efabless/raven-picorv32/verilog/raven_cam/cam.c

#include "cam.h"
#include "spi_io.h"
#include "i2c_io.h"

extern void print(const char *p);
extern void print_hex(uint32_t v, int digits);

void _delay_ms(int v) {
    for (int j = 0; j < 170 * v; j++);
}

bool check_spi() {
    uint8_t data;
    // test spi with write and read from test register
    write_spi_slave(0x00, 0x55);
    data = read_spi_slave_byte(0x00);
    if (data == 0x55) {
        return true;
    }
    return false;
}

bool check_camera(uint32_t *vid, uint32_t *pid) {
//    uint8_t vid, pid;
    write_sensor_reg(0xff, 0x01);
    read_sensor_reg(OV2640_CHIPID_HIGH, vid);
    read_sensor_reg(OV2640_CHIPID_LOW, pid);
    *vid &= (uint8_t) 0xff;
    *pid &= (uint8_t) 0xff;
    if ((*vid == 0x26 ) && ((*pid == 0x41 ) || (*pid == 0x42 )))
        return true;
    else
        return false;
}

void reset_cpld() {
    write_reg(0x07, 0x80);
    _delay_ms(1000);
    write_reg(0x07, 0x00);
    _delay_ms(1000);
}

void init_camera() {
    write_sensor_reg(0xff, 0x01);
    write_sensor_reg(0x12, 0x80);
    _delay_ms(1000);

    print("jpeg init\n");
    write_sensor_reg_list(OV2640_JPEG_INIT, true);

    print("yuv422\n");
    write_sensor_reg_list(OV2640_YUV422, true);

    print("ov2640 jpeg\n");
    write_sensor_reg_list(OV2640_JPEG, true);

    write_sensor_reg(0xff, 0x01);
    write_sensor_reg(0x15, 0x00);
    write_sensor_reg_list(OV2640_160x120_JPEG, true);
//    write_sensor_reg_list(OV2640_320x240_JPEG, true);
    write_sensor_reg(0xff, 0x00);
    write_sensor_reg(0x44, 0x32);

//    write_sensor_reg_list(OV2640_QVGA);
    _delay_ms(1000);

}

void set_frame_count() {
    write_reg(0x01, 0x00); // set frame count to 1
    write_reg(0x02, 0x00); // set LCD bus mode to MCU
    _delay_ms(1000);
}

void flush_fifo(void) {
	write_reg(ARDUCHIP_FIFO, FIFO_CLEAR_MASK);
//	write_reg(ARDUCHIP_FIFO, FIFO_RDPTR_RST_MASK);
//	write_reg(ARDUCHIP_FIFO, FIFO_RDPTR_RST_MASK | FIFO_WRPTR_RST_MASK);
}

void reset_fifo_read_ptr(void) {
	write_reg(ARDUCHIP_FIFO, FIFO_RDPTR_RST_MASK);
//	write_reg(ARDUCHIP_FIFO, FIFO_RDPTR_RST_MASK | FIFO_WRPTR_RST_MASK);
}

void start_capture(void) {
	write_reg(ARDUCHIP_FIFO, FIFO_START_MASK);
}

void clear_fifo_flag(void) {
	write_reg(ARDUCHIP_FIFO, FIFO_CLEAR_MASK);
}

uint8_t read_fifo(void) {}

uint8_t read_reg(uint32_t addr) {
    return read_spi_slave_byte(addr);
}

void write_reg(uint32_t addr, uint32_t data) {
    write_spi_slave(addr, data);
}

void write_sensor_reg(uint32_t addr, uint32_t data) {
    write_i2c_slave(SENSOR_ADDR, addr, data);
}

void read_sensor_reg(uint32_t addr, uint32_t* data) {
    *data = read_i2c_slave_byte(SENSOR_ADDR, addr) & (uint32_t) 0x00ff;
}

bool write_sensor_reg_list(const struct sensor_reg reglist[], bool verify) {
    uint32_t reg_addr = 0;
    uint32_t reg_val = 0, data;
    const struct sensor_reg *next = reglist;
    bool status = true;
    while ((reg_addr != 0xff) || (reg_val != 0xff))
    {
        reg_addr = next->reg;
        reg_val = next->val;
        write_sensor_reg(reg_addr, reg_val);
        if (verify) {
            read_sensor_reg(reg_addr, &data);
            if (data != reg_val) {
                print("error@0x"); print_hex(reg_addr, 2);
                print("=0x"); print_hex(data, 2);
                print(" ( 0x"); print_hex(reg_val, 2);
                print(" )\n");
                status = false;
            }
        }
        next++;
    }
    _delay_ms(1000);
    return status;
}

uint32_t read_fifo_length()
{
	uint32_t len1,len2,len3,length=0;
	len1 = read_reg(FIFO_SIZE1);
    len2 = read_reg(FIFO_SIZE2);
    len3 = read_reg(FIFO_SIZE3) & 0x7f;
    length = ((len3 << 16) | (len2 << 8) | len1) & 0x07fffff;
	return length;
}

bool set_JPEG_size(uint8_t size) {
    switch(size) {
        case OV2640_160x120:
            return write_sensor_reg_list(OV2640_160x120_JPEG, true);
        case OV2640_640x480:
            return write_sensor_reg_list(OV2640_640x480_JPEG, true);
        case OV2640_800x600:
            return write_sensor_reg_list(OV2640_800x600_JPEG, true);
        case OV2640_320x240:
        default:
            return write_sensor_reg_list(OV2640_320x240_JPEG, true);
    }

}

void set_Light_Mode(uint8_t Light_Mode) {}
void set_Color_Saturation(uint8_t Color_Saturation) {}
void set_Brightness(uint8_t Brightness) {}
void set_Contrast(uint8_t Contrast) {}
void set_Special_effects(uint8_t Special_effect) {}

const char bmp_header[BMPIMAGEOFFSET] PROGMEM =
{
  0x42, 0x4D, 0x36, 0x58, 0x02, 0x00, 0x00, 0x00, 0x00, 0x00, 0x42, 0x00, 0x00, 0x00, 0x28, 0x00,
  0x00, 0x00, 0x40, 0x01, 0x00, 0x00, 0xF0, 0x00, 0x00, 0x00, 0x01, 0x00, 0x10, 0x00, 0x03, 0x00,
  0x00, 0x00, 0x00, 0x58, 0x02, 0x00, 0xC4, 0x0E, 0x00, 0x00, 0xC4, 0x0E, 0x00, 0x00, 0x00, 0x00,
  0x00, 0x00, 0x00, 0x00, 0x00, 0x00, 0x00, 0xF8, 0x00, 0x00, 0xE0, 0x07, 0x00, 0x00, 0x1F, 0x00,
  0x00, 0x00
};

const struct sensor_reg OV2640_JPEG_INIT[] PROGMEM =
{
  { 0xff, 0x00 },
  { 0x2c, 0xff },
  { 0x2e, 0xdf },
  { 0xff, 0x01 },
  { 0x3c, 0x32 },
  { 0x11, 0x00 },
  { 0x09, 0x02 },
  { 0x04, 0x28 },
  { 0x13, 0xe5 },
  { 0x14, 0x48 },
  { 0x2c, 0x0c },
  { 0x33, 0x78 },
  { 0x3a, 0x33 },
  { 0x3b, 0xfB },
  { 0x3e, 0x00 },
  { 0x43, 0x11 },
  { 0x16, 0x10 },
  { 0x39, 0x92 },
  { 0x35, 0xda },
  { 0x22, 0x1a },
  { 0x37, 0xc3 },
  { 0x23, 0x00 },
  { 0x34, 0xc0 },
  { 0x36, 0x1a },
  { 0x06, 0x88 },
  { 0x07, 0xc0 },
  { 0x0d, 0x87 },
  { 0x0e, 0x41 },
  { 0x4c, 0x00 },
  { 0x48, 0x00 },
  { 0x5B, 0x00 },
  { 0x42, 0x03 },
  { 0x4a, 0x81 },
  { 0x21, 0x99 },
  { 0x24, 0x40 },
  { 0x25, 0x38 },
  { 0x26, 0x82 },
  { 0x5c, 0x00 },
  { 0x63, 0x00 },
  { 0x61, 0x70 },
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

  { 0x12, 0x40 },
  { 0xd3, 0x04 },	//{ 0xd3, 0x7f },
  { 0xc0, 0x16 },
  { 0xC1, 0x12 },
  { 0x8c, 0x00 },
  { 0x86, 0x3d },
  { 0x50, 0x00 },
  { 0x51, 0x2C },
  { 0x52, 0x24 },
  { 0x53, 0x00 },
  { 0x54, 0x00 },
  { 0x55, 0x00 },
  { 0x5A, 0x2c },
  { 0x5b, 0x24 },
  { 0x5c, 0x00 },
  { 0xff, 0xff },
};

const struct sensor_reg OV2640_JPEG[] PROGMEM =
{
  { 0xe0, 0x14 },
  { 0xe1, 0x77 },
  { 0xe5, 0x1f },
  { 0xd7, 0x03 },
  { 0xda, 0x10 },
  { 0xe0, 0x00 },
  { 0xFF, 0x01 },
  { 0x04, 0x08 },
  { 0xff, 0xff },
};

const struct sensor_reg OV2640_YUV422[] PROGMEM =
{
  { 0xFF, 0x00 },
  { 0x05, 0x00 },
  { 0xDA, 0x10 },
  { 0xD7, 0x03 },
  { 0xDF, 0x00 },
  { 0x33, 0x80 },
  { 0x3C, 0x40 },
  { 0xe1, 0x77 },
  { 0x00, 0x00 },
  { 0xff, 0xff },
};

/* JPG 160x120 */
const struct sensor_reg OV2640_160x120_JPEG[] PROGMEM =
{
  { 0xff, 0x01 },
  { 0x12, 0x40 },
  { 0x17, 0x11 },
  { 0x18, 0x43 },
  { 0x19, 0x00 },
  { 0x1a, 0x4b },
  { 0x32, 0x09 },
  { 0x4f, 0xca },
  { 0x50, 0xa8 },
  { 0x5a, 0x23 },
  { 0x6d, 0x00 },
  { 0x39, 0x12 },
  { 0x35, 0xda },
  { 0x22, 0x1a },
  { 0x37, 0xc3 },
  { 0x23, 0x00 },
  { 0x34, 0xc0 },
  { 0x36, 0x1a },
  { 0x06, 0x88 },
  { 0x07, 0xc0 },
  { 0x0d, 0x87 },
  { 0x0e, 0x41 },
  { 0x4c, 0x00 },
  { 0xff, 0x00 },
  { 0xe0, 0x04 },
  { 0xc0, 0x64 },
  { 0xc1, 0x4b },
  { 0x86, 0x35 },
  { 0x50, 0x92 },
  { 0x51, 0xc8 },
  { 0x52, 0x96 },
  { 0x53, 0x00 },
  { 0x54, 0x00 },
  { 0x55, 0x00 },
  { 0x57, 0x00 },
  { 0x5a, 0x28 },
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
	{0x0e, 0x01},

	{0xff, 0x00},
	{0xe0, 0x04},
	{0xc0, 0xc8},
	{0xc1, 0x96},
	{0x86, 0x3d},
	{0x50, 0x89},
	{0x51, 0x90},
	{0x52, 0x2c},
	{0x53, 0x00},
	{0x54, 0x00},
	{0x55, 0x88},
	{0x57, 0x00},
	{0x5a, 0xa0},
	{0x5b, 0x78},
	{0x5c, 0x00},
	{0xd3, 0x04},
	{0xe0, 0x00},

  	{0xff, 0xff},
};

const struct sensor_reg OV2640_800x600_JPEG[] PROGMEM =
{
	{0xff, 0x01},
	{0x11, 0x01},
	{0x12, 0x00}, // Bit[6:4]: Resolution selection//0x02Ϊ����
	{0x17, 0x11}, // HREFST[10:3]
	{0x18, 0x75}, // HREFEND[10:3]
	{0x32, 0x36}, // Bit[5:3]: HREFEND[2:0]; Bit[2:0]: HREFST[2:0]
	{0x19, 0x01}, // VSTRT[9:2]
	{0x1a, 0x97}, // VEND[9:2]
	{0x03, 0x0f}, // Bit[3:2]: VEND[1:0]; Bit[1:0]: VSTRT[1:0]
	{0x37, 0x40},
	{0x4f, 0xbb},
	{0x50, 0x9c},
	{0x5a, 0x57},
	{0x6d, 0x80},
	{0x3d, 0x34},
	{0x39, 0x02},
	{0x35, 0x88},
	{0x22, 0x0a},
	{0x37, 0x40},
	{0x34, 0xa0},
	{0x06, 0x02},
	{0x0d, 0xb7},
	{0x0e, 0x01},

	{0xff, 0x00},
	{0xe0, 0x04},
	{0xc0, 0xc8},
	{0xc1, 0x96},
	{0x86, 0x35},
	{0x50, 0x89},
	{0x51, 0x90},
	{0x52, 0x2c},
	{0x53, 0x00},
	{0x54, 0x00},
	{0x55, 0x88},
	{0x57, 0x00},
	{0x5a, 0xc8},
	{0x5b, 0x96},
	{0x5c, 0x00},
	{0xd3, 0x02},
	{0xe0, 0x00},

  	{0xff, 0xff},
};
