efabless/raven-picorv32/verilog/raven_cam/i2c_io.c

#include "../raven_defs.h"
#include "i2c_io.h"

#define SDA_PIN (uint32_t) (1 << 14) // bit 14
#define SCL_PIN (uint32_t) (1 << 15) // bit 15

#define SCL_OUT (volatile uint32_t) ((reg_gpio_ena) &= ~(SCL_PIN))
#define SCL_IN (volatile uint32_t) (reg_gpio_ena |= (SCL_PIN))
#define SDA_OUT (volatile uint32_t) ((reg_gpio_ena) &= ~(SDA_PIN))
#define SDA_IN (volatile uint32_t) (reg_gpio_ena |= (SDA_PIN))

#define SCL_HIGH SCL_IN
#define SCL_LOW SCL_OUT; (volatile uint32_t) ((reg_gpio_data) &= ~(SCL_PIN))
#define SCL_READ (volatile uint32_t) ((reg_gpio_data) & (SCL_PIN))
#define SDA_HIGH SDA_IN
#define SDA_LOW SDA_OUT; (volatile uint32_t) ((reg_gpio_data) &= ~(SDA_PIN))
#define SDA_READ (volatile uint32_t) ((reg_gpio_data) & (SDA_PIN))

void i2c_delay()
{

//  I2C standard mode (100k) = 5 usec min hold time

//	for (int j = 0; j < 200000; j++);  // 1 secs
//	for (int j = 0; j < 100000; j++);  // 0.5 secs
	for (int j = 0; j < 1; j++);  // ~23 usec (measured)

}

void i2c_init()
{
    // enable internal pull-up and disable internal pull-down resistors
    reg_gpio_pu &= ~(SCL_PIN & SDA_PIN);
    reg_gpio_pd |= SCL_PIN & SDA_PIN;

    SDA_HIGH;
    SCL_HIGH;
    i2c_delay();
}

void i2c_start()
{
    SDA_HIGH;
    SCL_HIGH;
    i2c_delay();
    SDA_LOW;
    i2c_delay();
    SCL_LOW;
    i2c_delay();
}

void i2c_stop ()
{
    SDA_LOW;
    i2c_delay();
    SCL_HIGH;
    i2c_delay();
    SDA_HIGH;
    i2c_delay();
}

void i2c_write_bit(volatile uint32_t b)
{
    volatile uint32_t clk;

    if ( b > 0 )
        SDA_HIGH;
    else
        SDA_LOW;

    i2c_delay();

    SCL_HIGH;

    // clock stretching
    SCL_IN; clk = SCL_READ;
    while (!clk)
        clk = SCL_READ;

    i2c_delay();
    SCL_LOW;

}

volatile uint32_t i2c_read_bit()
{

    volatile uint32_t b;
    volatile uint32_t clk;

    SDA_HIGH;
    i2c_delay();
    SCL_HIGH;

    // clock stretching
    SCL_IN; clk = SCL_READ;
    while (!clk)
        clk = SCL_READ;

    i2c_delay();

    SDA_IN;
    if ( SDA_READ)
        b = 1;
    else
        b = 0;

    SCL_LOW;

    return b;
}

bool i2c_write(volatile uint32_t data)
{
    uint32_t ack;

 	/* 8 bits */
	for (int i = 0; i < 8; i++)
	{
	    i2c_write_bit(data & (uint32_t) 0x0080);
      	data  <<= 1;
	}

	ack = i2c_read_bit();

	return ack;
}

volatile uint32_t i2c_read(bool ack)
{
	volatile uint32_t data;

//    print_ln("i2c_read()...");
	data = 0x0000;
	for (int i = 0; i < 8; i++)
	{
		data <<= 1;
      	data |= i2c_read_bit();
	}

	if (ack)
	    i2c_write_bit(0);
	else
	    i2c_write_bit(1);

   return data;
}

void write_i2c_slave(volatile uint32_t slave_addr, volatile uint32_t word_addr, volatile uint32_t data)
{
  	i2c_start();
   	i2c_write(slave_addr);
    i2c_write(word_addr);
   	i2c_write(data);
   	i2c_stop();
}

uint32_t read_i2c_slave_byte(volatile uint32_t slave_addr, volatile uint32_t word_addr)
{
   	volatile uint32_t data;

  	i2c_start();
   	i2c_write(slave_addr);
    i2c_write(word_addr);

    i2c_start();
    i2c_write(slave_addr | (uint32_t) 0x0001);  // addr + read mode
	data = i2c_read(false);
	i2c_stop();

   	return data;
}

void read_i2c_slave_bytes(volatile uint32_t slave_addr, volatile uint32_t word_addr, volatile uint32_t *data, int len)
{
   	int i;

  	i2c_start();
   	i2c_write(slave_addr);
   	i2c_write(word_addr);

    i2c_start();
    i2c_write(slave_addr | (uint32_t) 0x0001);  // addr + read mode
    for (i = 0; i < len-1; i++)
	    data[i] = i2c_read(true);
	data[len-1] = i2c_read(false);
	i2c_stop();
}
