efabless/raven-picorv32/verilog/raven_rtc/i2c_io.h

#ifndef I2C_IO_H
#define I2C_IO_H
#include "../raven_defs.h"

#define RTC_I2C_ADDR (uint32_t) 0xA2 // RTC PCF8563
//#define RTC_I2C_ADDR (uint32_t)0xD0 // RTC DS3231

void write_i2c_slave(volatile uint32_t slave_addr, volatile uint32_t word_addr, volatile uint32_t data);
uint32_t read_i2c_slave_byte(volatile uint32_t slave_addr, volatile uint32_t word_addr);
void read_i2c_slave_bytes(volatile uint32_t slave_addr, volatile uint32_t word_addr, volatile uint32_t *data, int len);
void i2c_init();
void i2c_start();
void i2c_stop();
bool i2c_write(volatile uint32_t data);
uint32_t i2c_read(bool ack);

#endif // I2C_IO_H
